bookofthefuture/ev-gauge/ev_gauge/data/launch.bmp

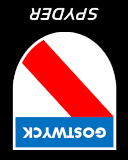
ev_gauge/data/launch.bmp
