bookofthefuture/ev-gauge/ev_gauge/ev_diy_font.h

/////////
// Font: ev_diy_font (22px)
// Size: approx 2.4 kB in flash
// exported with Adafruit GFX font editor (https://github.com/rOzzy1987/gfx-font-editor)

#pragma once
#include <Adafruit_GFX.h>
#include <Arduino.h>


const uint8_t ev_diy_font_Bitmap[] PROGMEM  = {
    0xff, 0xff, 0xfe, 0x48, 0x7e, 0xef, 0xdf, 0xbf, 0x74, 0x40, 0x19, 0x86, 0x67, 0xfd, 0xff, 0x33,
    0x0c, 0xc3, 0x33, 0xfe, 0xff, 0x99, 0x86, 0x61, 0x90, 0x10, 0x1f, 0x1f, 0xde, 0xff, 0x3f, 0x83,
    0xc0, 0xfc, 0x1f, 0x09, 0xfc, 0xfe, 0xf7, 0xf1, 0xe0, 0x40, 0x38, 0x10, 0x7c, 0x30, 0xc6, 0x20,
    0xc6, 0x40, 0xc6, 0x40, 0x7c, 0x80, 0x39, 0x9c, 0x01, 0x3e, 0x03, 0x63, 0x02, 0x63, 0x04, 0x63,
    0x0c, 0x3e, 0x08, 0x1c, 0x0e, 0x01, 0xf8, 0x3b, 0x83, 0xb8, 0x3f, 0x01, 0xe0, 0x3e, 0x67, 0x76,
    0xe3, 0xee, 0x1c, 0xf3, 0xc7, 0xfe, 0x3f, 0x70, 0xff, 0xf4, 0x18, 0x63, 0x1c, 0x73, 0x8e, 0x38,
    0xe3, 0x8e, 0x18, 0x70, 0xc3, 0x06, 0x08, 0x61, 0x83, 0x0e, 0x38, 0x71, 0xc7, 0x1c, 0x71, 0xc6,
    0x38, 0xe3, 0x18, 0x40, 0x21, 0x3e, 0x45, 0x28, 0x38, 0x70, 0xe7, 0xff, 0xe7, 0x0e, 0x1c, 0xfc,
    0x9c, 0xff, 0xc0, 0x08, 0xc4, 0x23, 0x10, 0x84, 0x62, 0x11, 0x88, 0x00, 0x3e, 0x3f, 0x9d, 0xdc,
    0x7e, 0x3f, 0x1f, 0x8f, 0xc7, 0xe3, 0xf1, 0xdd, 0xcf, 0xe3, 0xe0, 0x08, 0xff, 0xf3, 0x9c, 0xe7,
    0x39, 0xce, 0x73, 0x80, 0x3e, 0x3f, 0xb8, 0xfc, 0x70, 0x38, 0x1c, 0x1c, 0x1c, 0x1c, 0x1c, 0x1c,
    0x0f, 0xf7, 0xf8, 0x3c, 0x7f, 0xe7, 0xe7, 0x07, 0x0c, 0x0e, 0x07, 0x07, 0xe7, 0xe7, 0x7e, 0x3c,
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
    { 1366, 24, 24, 0, 0, -24 },        // char '' 0x82 (130)
    { 1438, 24, 24, 0, 0, -24 },        // char '' 0x83 (131)
}; // 900 bytes

const GFXfont ev_diy_font PROGMEM  = { (uint8_t*) ev_diy_font_Bitmap, (GFXglyph*) ev_diy_font_Glyphs, 32, 131, 22 };
